karuru6225/car-iot-services/car_iot_android/DESIGN.md

# UIデザインの指針（car_iot_android）

このアプリのUIを作り直す/拡張するときの指針。2026/08のデザイン刷新で、**配色を3回
作り直して**ようやく形になった過程で得たものを残す。同じ回り道を繰り返さないための文書。

対象読者は、このリポジトリでUIを触るエージェント/開発者。

---

## 0. 前提: このアプリの被写体

**走行中に一瞥して読む車載計器**。デスクでじっくり眺める管理画面ではない。

この一文が全ての判断の根拠になる。迷ったら「実車の計器はどうなっているか」に戻る。

---

## 1. 3回失敗した記録（読み飛ばさないこと）

| 版 | やったこと | なぜ駄目だったか |
|---|---|---|
| 1. レーシング/ミニマル | Material3の`ColorScheme`だけ差し替え | ウィジェットは標準のまま。ピル型ボタン・太いProgressIndicatorが残り「Material3そのまま」の印象を脱していない |
| 2. shadcn/ui | 公式トークンをOKLCHから変換して忠実に移植 | 体系としては正しく動いたが、**Web管理画面のデザイン言語を車載計器に持ち込んだ**結果、グレー一色の事務的なUIになった |
| 3. 計器盤ベース（現行） | 形・タイポ・配色を計器の語彙で作り直し | — |

**1と2に共通する失敗**: 「数値を見せる計器」ではなく「**数値も出る設定アプリ**」を
作っていた。ラベル11sp・数値22〜30spと差が小さく、数値が主役になっていなかった。

デザインシステムを持ってくること自体は悪くない。**被写体と噛み合うかを先に問う**こと。

---

## 2. 形が先、色が後

配色だけ変えてもMaterial3の印象は抜けない。実際に効いたのは形の方だった。

- **Material3の`Button`は`Shapes`ではなく`CircleShape`固定**。テーマ側で`Shapes`を
  差し替えてもピル型のまま変わらない。`shape = ClusterButtonShape`を各ボタンに明示的に
  渡す必要がある（ハマりどころ）
- **`LinearProgressIndicator`/`CircularProgressIndicator`は使わない**。あれは「進捗」の
  表現で、計測値に進捗の概念は無い（電圧は0%から100%へ進行しない）。太い塗り面が
  数値より目立つのも良くない。レンジ内の位置は`ValueRail`（1dpのヘアライン＋2dpの
  ティック）で示す
- **テーマは配色だけでなく描かれ方も切り替えられる**。`InstrumentStyle`
  （FLAT/ANALOG）を`CompositionLocal`で配り、GAUGEテーマだけ針と目盛りのアナログ
  ダイヤルになる。ただしユーザーが選ぶゲージ種別（CIRCULAR/BAR等）は上書きしない。
  「CIRCULARが**どう描かれるか**」だけをテーマが決める

---

## 3. タイポグラフィの落差が核

計器盤は**極小のラベル**と**巨大な数値**の落差で出来ている。ここを最大に開く。

```
ラベル   10sp / letterSpacing +2.5sp   （小さく、字間を空ける）
ヒーロー 60sp / letterSpacing -2sp     （大きく、字間を詰める）
```

- 数値は**等幅かつ細字**。桁が動かず、大きくしても圧迫感が出ない。太字は使わない
  （アナログ計器の数字は太くない）
- **単位は数値に従属**する情報。極小・くすませてベースラインに沿わせる。数値と同じ
  大きさで出すとせっかくの落差が崩れる

---

## 4. 量産されがちな配色を避ける

いま生成されるUIは配色が3パターンに収束しがち:

1. クリーム地（#F4F1EA付近）＋高コントラストのセリフ＋テラコッタ
2. ほぼ黒の地＋鮮やかなアシッドグリーン/バーミリオン1色
3. ブロードシート風（ヘアライン罫・角丸ゼロ・新聞的な段組）

**被写体由来の語彙を使えば自然に外れる。** このアプリでは「夜間の自動車メーター照明は
実際に暖色アンバー」という事実からアンバーを選んだ。地色を純黒でなく青みのある
`#06080C`にしたのも、クラスターがガラス越しに冷たく沈んで見えることに倣ったもの。

---

## 5. 意味のない装飾は入れない

構造や装飾は**内容について本当のことを符号化**しているときだけ置く。

実際に**入れなかった**もの:

- **レッドゾーン** … タコメーターらしさは出るが、電圧や水温では「上限側＝危険」という
  意味を持たない。意味のない装飾になる
- クローム風グラデーション/ガラスの映り込み/針の影 … 質感の演出であって情報ではない

逆に**入れた**もの（意味があるから）:

- 主目盛り/副目盛りの階層と、**実際に刻まれた数字** … これが計器に見えるかを決める。
  円弧に棒を1本生やしただけでは円いプログレスバーにしか見えない
- 目盛りの数字を**キリのいい値に丸める** … 実レンジを素直に4等分すると
  0/1750/3500/5250/7000と半端になる。実車の計器は0/2000/4000/6000/8000のような
  刻みを持ち、そのぶん上限がレンジより広い（7000rpmの車に0-8000の文字盤）

---

## 6. プレースホルダー状態だけで判断しない

BLE未接続だと計測値は常にnullで、`--.---`しか見られない。**この状態でデザインの
良し悪しは判断できない。**

`CONTEXT.md`の「エミュレータでUIを確認する際のダミー値注入」に手順がある。要点:

- `state/CarIotState.kt`の`_measurement`/`_obdReading`/`_obdHistory`の初期値を一時的に書き換える
- `meter/MeterConfigStore.kt`の`load()`冒頭で`defaultSlots()`を即returnさせると
  ゲージ4種を一度に確認できる
- 注入行には必ず`// TODO: デザイン確認用ダミー値(戻すこと)`を付け、撤去後に
  `grep -rn "デザイン確認用" app/src/` と `git status` の**両方**で確認する

この手法で実際に見つけた不具合:

- 円弧ゲージが描画ボックスをはみ出して下半分が切れていた（プレースホルダーでは気づけない）
- 単位が数値と同じ大きさで出てラベル/数値の落差が崩れていた
- ミニグラフがほぼ平坦な直線だった（後述）

---

## 7. 視認性は数値で検証する（WCAG）

感覚で決めない。詳細は`CONTEXT.md`の「配色はWCAGのコントラスト比で検証する」。

| 対象 | 必要比 |
|---|---|
| 数値（大きい文字） | 3.0:1 |
| ラベル・本文・見出し・ボタン文字 | 4.5:1 |
| レール軌道・針・ティック・ボタン枠 | 3.0:1 |

**この検証で分かった重要な点:**

- **暗色同士の破綻は目視で気づけない**。ユーザーが気づいたのはDAYの3.50:1だったが、
  実際にはNIGHTのレールが**1.17:1**でほぼ不可視だった。全テーマで数値を出すこと
- **アクセント色を小さな文字に使うのは脆い**。DAY/GAUGEでは、見出しが4.5:1を満たす
  明度とボタン文字（白）が4.5:1を満たす明度が**両立しなかった**。アクセントは
  **図形（針・ティック）と塗りボタンに限定**し、見出し・値は前景色にする。
  実際の計器も刻印は白で色が乗るのは針だけなので、語彙としても整合する
- 比較する背景は**実際に乗る面**を使う。`Card`は`surfaceContainerHighest`、
  `OutlinedCard`と画面地は`surface`。`background`と比べても意味がない

---

## 8. フォントサイズ設定への耐性（WCAG 1.4.4）

`adb shell settings put system font_scale 1.5`（戻すときは`1.0`）で確認する。
計算では出ないので実際に拡大して見るしかない。

1.5倍で見つかった不具合:

- **数値が黙って切り捨てられていた**。`maxLines = 1`の既定overflowは`Clip`なので
  `13.812`が`13.81`になり省略記号も出ない。**崩れて見えるのではなく「別の正しそうな値」
  に見える**ため、計測値としては誤読を生む。`AutoSizeValueText`で枠に収まるまで縮小し、
  全桁を残す
- **Canvasの文字だけ拡大しなかった**。`android.graphics.Paint`の`textSize`に`dp`を
  渡していたため。**文字サイズは必ず`sp`**。ただし文字盤のように直径が決まっている
  場合は上限で頭打ちにしないと突き破る

固定幅のタイルに数値を出す箇所を追加するときは、この2点を必ず確認すること。

---

## 9. データ可視化はデータのレンジに合わせる

ミニグラフ（スパークライン）の縦軸に**メーターのレンジを使ってはいけない**。

ECU電圧のレンジは10-16Vだが実走行の揺れは13.8-14.4V程度で、レンジ基準だとグラフ
高さの1割しか使わず**ほぼ平坦な直線**にしかならない。ミニグラフは絶対値ではなく
**変化の形**を見るためのもの（絶対値はすぐ上に数値で出ている）。

ただし完全にデータ任せにすると、値がほぼ一定のときにセンサーノイズが画面いっぱいの
山脈に化ける。**メーターレンジの2%を下限の振れ幅として確保**し、それ以下の変動は
平坦なままにする。

---

## 10. 進め方

1. **被写体を一文で言う**。「走行中に一瞥して読む車載計器」。ここから全部を導く
2. **実物の語彙を調べる**。色・形・比率・書体。思いつきより実在の参照が強い
3. **形から作る**。配色だけ変えても印象は変わらない
4. **ダミー値を入れて見る**。プレースホルダーでは判断できない
5. **スクリーンショットを撮って自己批評する**。文章で考えるより早く欠陥が見つかる
6. **数値で検証する**。コントラスト比、フォントスケール1.5倍
7. **一つ減らす**。装飾を足す前に、意味を持たない要素を外せないか見る

`frontend-design`スキルが入っている環境ならそれも使う。ただし**スキルを呼ぶだけでは
足りない** — 被写体の語彙を自分で調べ、スクリーンショットで自己批評する工程が要る。

---

## 参照

- `CONTEXT.md` — 実装状態・実機検証メモ・ダミー注入とWCAG検証の具体手順
- `docs/car_iot_android_plan.md` — 全体設計・フェーズのロードマップ・刷新の経緯
- `ui/theme/` — 3テーマの配色・タイポ・角丸の定義
- `ui/meter/AnalogDial.kt` — 目盛りと針の描き方（何を描き、何を描かないか）
- `ui/meter/ValueRail.kt` — 署名要素。ProgressIndicatorを置き換えた理由
