karuru6225/car-iot-services/esp32_iot_gateway/OBD_PID_WIKIPEDIA.md

# OBD-II PID リファレンス（Wikipedia 日本語訳）

出典: [Wikipedia - OBD-II PIDs](https://en.wikipedia.org/wiki/OBD-II_PIDs)（SAE J1979 / ISO 15031-5 準拠）

> **注意**: メーカーはすべてのサービス・PID をサポートする義務はない。
> Honda N-VAN 固有の対応状況は `OBD.md` および `CAN_REFERENCE.md` を参照。

---

## 変数の定義

レスポンスバイトは A（最初）、B、C、D の順で参照する。

| 変数 | 意味 |
|---|---|
| A | レスポンス data[3]（最初のデータバイト） |
| B | レスポンス data[4] |
| C | レスポンス data[5] |
| D | レスポンス data[6] |

---

## Mode 01 — 現在データ取得（Show Current Data）

リクエスト: `Byte0=0x02 Byte1=0x01 Byte2=PID`  
レスポンス: `Byte1=0x41 Byte2=PID Byte3=A Byte4=B ...`

### 0x00〜0x1F

| PID | バイト数 | 名称 | 最小 | 最大 | 単位 | デコード式 |
|-----|---|---|---|---|---|---|
| 0x00 | 4 | サポートPID一覧 [0x01〜0x20] | — | — | — | ビットマスク |
| 0x01 | 4 | 診断コード消去後のモニタ状態 | — | — | — | ビットエンコード |
| 0x02 | 2 | フリーズフレームを記録させたDTC | — | — | — | Service 03 と同形式 |
| 0x03 | 2 | 燃料システム状態 | — | — | — | 列挙値 |
| 0x04 | 1 | 計算エンジン負荷 | 0 | 100 | % | `A / 2.55` |
| 0x05 | 1 | エンジン冷却水温 | -40 | 215 | °C | `A - 40` |
| 0x06 | 1 | 短期燃料トリム Bank1 | -100 | 99.2 | % | `(A / 1.28) - 100` |
| 0x07 | 1 | 長期燃料トリム Bank1 | -100 | 99.2 | % | `(A / 1.28) - 100` |
| 0x08 | 1 | 短期燃料トリム Bank2 | -100 | 99.2 | % | `(A / 1.28) - 100` |
| 0x09 | 1 | 長期燃料トリム Bank2 | -100 | 99.2 | % | `(A / 1.28) - 100` |
| 0x0A | 1 | 燃料圧力（ゲージ圧） | 0 | 765 | kPa | `3 × A` |
| 0x0B | 1 | 吸気管絶対圧（MAP） | 0 | 255 | kPa | `A` |
| 0x0C | 2 | エンジン回転数（RPM） | 0 | 16383.75 | rpm | `(256A + B) / 4` |
| 0x0D | 1 | 車速 | 0 | 255 | km/h | `A` |
| 0x0E | 1 | 点火タイミング進角 | -64 | 63.5 | °BTDC | `(A / 2) - 64` |
| 0x0F | 1 | 吸気温度 | -40 | 215 | °C | `A - 40` |
| 0x10 | 2 | MAF 空気流量 | 0 | 655.35 | g/s | `(256A + B) / 100` |
| 0x11 | 1 | スロットル開度 | 0 | 100 | % | `A / 2.55` |
| 0x12 | 1 | セカンダリエアシステム状態 | — | — | — | 列挙値 |
| 0x13 | 1 | O2 センサ搭載位置（2バンク） | — | — | — | ビットエンコード |
| 0x14 | 2 | O2 センサ1: 電圧 / 短期燃料トリム | 0 / -100 | 1.275 / 99.2 | V / % | `A / 200`（電圧）; `(B / 1.28) - 100`（トリム） |
| 0x15 | 2 | O2 センサ2: 電圧 / STFT | 同上 | 同上 | V / % | 同上 |
| 0x16 | 2 | O2 センサ3: 電圧 / STFT | 同上 | 同上 | V / % | 同上 |
| 0x17 | 2 | O2 センサ4: 電圧 / STFT | 同上 | 同上 | V / % | 同上 |
| 0x18 | 2 | O2 センサ5: 電圧 / STFT | 同上 | 同上 | V / % | 同上 |
| 0x19 | 2 | O2 センサ6: 電圧 / STFT | 同上 | 同上 | V / % | 同上 |
| 0x1A | 2 | O2 センサ7: 電圧 / STFT | 同上 | 同上 | V / % | 同上 |
| 0x1B | 2 | O2 センサ8: 電圧 / STFT | 同上 | 同上 | V / % | 同上 |
| 0x1C | 1 | 準拠OBD規格 | 1 | 250 | — | 列挙値 |
| 0x1D | 1 | O2 センサ搭載位置（4バンク） | — | — | — | ビットエンコード |
| 0x1E | 1 | 補助入力状態 | — | — | — | ビットエンコード |
| 0x1F | 2 | エンジン始動後経過時間 | 0 | 65535 | s | `256A + B` |

### 0x20〜0x3F

| PID | バイト数 | 名称 | 最小 | 最大 | 単位 | デコード式 |
|-----|---|---|---|---|---|---|
| 0x20 | 4 | サポートPID一覧 [0x21〜0x40] | — | — | — | ビットマスク |
| 0x21 | 2 | MIL 点灯中の走行距離 | 0 | 65535 | km | `256A + B` |
| 0x22 | 2 | 燃料レール圧力（マニホールド相対） | 0 | 5177.265 | kPa | `0.079 × (256A + B)` |
| 0x23 | 2 | 燃料レールゲージ圧（ディーゼル/GDI） | 0 | 655350 | kPa | `10 × (256A + B)` |
| 0x24 | 4 | O2 センサ1: 空燃比λ / 電圧 | — | — | ratio / V | `(2/65536) × (256A+B)`（λ）; `(8/65536) × (256C+D)`（V） |
| 0x25 | 4 | O2 センサ2: λ / 電圧 | — | — | ratio / V | 同上 |
| 0x26 | 4 | O2 センサ3: λ / 電圧 | — | — | ratio / V | 同上 |
| 0x27 | 4 | O2 センサ4: λ / 電圧 | — | — | ratio / V | 同上 |
| 0x28 | 4 | O2 センサ5: λ / 電圧 | — | — | ratio / V | 同上 |
| 0x29 | 4 | O2 センサ6: λ / 電圧 | — | — | ratio / V | 同上 |
| 0x2A | 4 | O2 センサ7: λ / 電圧 | — | — | ratio / V | 同上 |
| 0x2B | 4 | O2 センサ8: λ / 電圧 | — | — | ratio / V | 同上 |
| 0x2C | 1 | EGR 指令値 | 0 | 100 | % | `A / 2.55` |
| 0x2D | 1 | EGR エラー | -100 | 99.2 | % | `(A / 1.28) - 100` |
| 0x2E | 1 | エバポパージ指令値 | 0 | 100 | % | `A / 2.55` |
| 0x2F | 1 | 燃料タンク残量 | 0 | 100 | % | `A / 2.55` |
| 0x30 | 1 | コード消去後のウォームアップ回数 | 0 | 255 | — | `A` |
| 0x31 | 2 | コード消去後の走行距離 | 0 | 65535 | km | `256A + B` |
| 0x32 | 2 | エバポシステム蒸気圧 | -8192 | 8191.75 | Pa | `(256A + B) / 4`（符号付き） |
| 0x33 | 1 | 大気圧（絶対） | 0 | 255 | kPa | `A` |
| 0x34 | 4 | O2 センサ1: λ / 電流 | 0 / -128 | <2 / <128 | ratio / mA | `(2/65536) × (256A+B)`（λ）; `((256C+D)/256) - 128`（mA） |
| 0x35 | 4 | O2 センサ2: λ / 電流 | — | — | ratio / mA | 同上 |
| 0x36 | 4 | O2 センサ3: λ / 電流 | — | — | ratio / mA | 同上 |
| 0x37 | 4 | O2 センサ4: λ / 電流 | — | — | ratio / mA | 同上 |
| 0x38 | 4 | O2 センサ5: λ / 電流 | — | — | ratio / mA | 同上 |
| 0x39 | 4 | O2 センサ6: λ / 電流 | — | — | ratio / mA | 同上 |
| 0x3A | 4 | O2 センサ7: λ / 電流 | — | — | ratio / mA | 同上 |
| 0x3B | 4 | O2 センサ8: λ / 電流 | — | — | ratio / mA | 同上 |
| 0x3C | 2 | 触媒温度: Bank1 Sensor1 | -40 | 6513.5 | °C | `((256A + B) / 10) - 40` |
| 0x3D | 2 | 触媒温度: Bank2 Sensor1 | -40 | 6513.5 | °C | `((256A + B) / 10) - 40` |
| 0x3E | 2 | 触媒温度: Bank1 Sensor2 | -40 | 6513.5 | °C | 同上 |
| 0x3F | 2 | 触媒温度: Bank2 Sensor2 | -40 | 6513.5 | °C | 同上 |

### 0x40〜0x5F

| PID | バイト数 | 名称 | 最小 | 最大 | 単位 | デコード式 |
|-----|---|---|---|---|---|---|
| 0x40 | 4 | サポートPID一覧 [0x41〜0x60] | — | — | — | ビットマスク |
| 0x41 | 4 | 今回ドライブサイクルのモニタ状態 | — | — | — | ビットエンコード |
| 0x42 | 2 | コントロールモジュール電圧（ECU電圧） | 0 | 65.535 | V | `(256A + B) / 1000` |
| 0x43 | 2 | 絶対負荷値 | 0 | 25700 | % | `(100 / 255) × (256A + B)` |
| 0x44 | 2 | 指令空燃比λ | 0 | <2 | ratio | `(2 / 65536) × (256A + B)` |
| 0x45 | 1 | 相対スロットル開度 | 0 | 100 | % | `A / 2.55` |
| 0x46 | 1 | 外気温 | -40 | 215 | °C | `A - 40` |
| 0x47 | 1 | 絶対スロットル開度 B | 0 | 100 | % | `A / 2.55` |
| 0x48 | 1 | 絶対スロットル開度 C | 0 | 100 | % | `A / 2.55` |
| 0x49 | 1 | アクセルペダル位置 D | 0 | 100 | % | `A / 2.55` |
| 0x4A | 1 | アクセルペダル位置 E | 0 | 100 | % | `A / 2.55` |
| 0x4B | 1 | アクセルペダル位置 F | 0 | 100 | % | `A / 2.55` |
| 0x4C | 1 | スロットルアクチュエータ指令値 | 0 | 100 | % | `A / 2.55` |
| 0x4D | 2 | MIL 点灯時間 | 0 | 65535 | min | `256A + B` |
| 0x4E | 2 | コード消去後の経過時間 | 0 | 65535 | min | `256A + B` |
| 0x4F | 4 | 複数パラメータの最大値 | — | — | — | A; B; C; D×10 |
| 0x50 | 4 | MAF 最大空気流量 | 0 | 2550 | g/s | `A × 10` |
| 0x51 | 1 | 燃料種別 | — | — | — | 列挙値 |
| 0x52 | 1 | エタノール混合率 | 0 | 100 | % | `A / 2.55` |
| 0x53 | 2 | エバポシステム蒸気圧（絶対） | 0 | 327.675 | kPa | `(256A + B) / 200` |
| 0x54 | 2 | エバポシステム蒸気圧（符号付き） | -32768 | 32767 | Pa | `256A + B`（符号付き） |
| 0x55 | 2 | セカンダリO2 短期燃料トリム | -100 | 99.2 | % | `(A / 1.28) - 100`; `(B / 1.28) - 100` |
| 0x56 | 2 | セカンダリO2 長期燃料トリム | -100 | 99.2 | % | 同上 |
| 0x57 | 2 | セカンダリO2 短期燃料トリム（Bank3/4） | -100 | 99.2 | % | 同上 |
| 0x58 | 2 | セカンダリO2 長期燃料トリム（Bank3/4） | -100 | 99.2 | % | 同上 |
| 0x59 | 2 | 燃料レール絶対圧 | 0 | 655350 | kPa | `10 × (256A + B)` |
| 0x5A | 1 | アクセルペダル相対位置 | 0 | 100 | % | `A / 2.55` |
| 0x5B | 1 | HVバッテリー残量 | 0 | 100 | % | `A / 2.55` |
| 0x5C | 1 | エンジンオイル温度 | -40 | 210 | °C | `A - 40` |
| 0x5D | 2 | 燃料噴射タイミング | -210 | 301.992 | ° | `((256A + B) / 128) - 210` |
| 0x5E | 2 | エンジン燃料消費率 | 0 | 3212.75 | L/h | `(256A + B) / 20` |
| 0x5F | 1 | 排出ガス規制要件 | — | — | — | ビットエンコード |

### 0x60〜0x7F

| PID | バイト数 | 名称 | 最小 | 最大 | 単位 | デコード式 |
|-----|---|---|---|---|---|---|
| 0x60 | 4 | サポートPID一覧 [0x61〜0x80] | — | — | — | ビットマスク |
| 0x61 | 1 | ドライバ要求トルク | -125 | 130 | % | `A - 125` |
| 0x62 | 1 | 実際のエンジントルク | -125 | 130 | % | `A - 125` |
| 0x63 | 2 | エンジン基準トルク | 0 | 65535 | N·m | `256A + B` |
| 0x64 | 5 | エンジントルクデータ（5点） | -125 | 130 | % | `A-125`; `B-125`; `C-125`; `D-125`; `E-125` |
| 0x65 | 2 | 補助入出力サポート情報 | — | — | — | ビットエンコード |
| 0x66 | 5 | MAF センサ（拡張、2センサ） | 0 | 2047.97 | g/s | `(256B + C) / 32`（S1）; `(256D + E) / 32`（S2） |
| 0x67 | 3 | 冷却水温（拡張、2センサ） | -40 | 215 | °C | `B - 40`（S1）; `C - 40`（S2） |
| 0x68 | 3 | 吸気温センサ（拡張） | -40 | 215 | °C | `B - 40`（S1）; `C - 40`（S2） |
| 0x69 | 7 | EGR 実値/指令値/誤差 | — | — | — | — |
| 0x6A | 5 | ディーゼル吸気空気流量制御 | — | — | — | — |
| 0x6B | 5 | EGR 温度 | — | — | — | — |
| 0x6C | 5 | スロットルアクチュエータ指令制御 | — | — | — | — |
| 0x6D | 11 | 燃料圧力制御システム | — | — | — | — |
| 0x6E | 9 | 噴射圧力制御システム | — | — | — | — |
| 0x6F | 3 | ターボコンプレッサ入口圧力 | — | — | — | — |
| 0x70 | 10 | ブースト圧制御 | 0 | 2047.97 | kPa | `(256D + E) / 0.03125` |
| 0x71 | 6 | 可変ジオメトリターボ（VGT）制御 | — | — | — | — |
| 0x72 | 5 | ウェイストゲート制御 | — | — | — | — |
| 0x73 | 5 | 排気圧力 | — | — | — | — |
| 0x74 | 5 | ターボチャージャ回転数 | — | — | — | — |
| 0x75 | 7 | ターボチャージャ温度（Bank1） | — | — | — | — |
| 0x76 | 7 | ターボチャージャ温度（Bank2） | — | — | — | — |
| 0x77 | 5 | チャージエアクーラ温度（CACT） | — | — | — | — |
| 0x78 | 9 | 排気ガス温度（EGT）Bank1 | — | — | — | 専用フォーマット |
| 0x79 | 9 | 排気ガス温度（EGT）Bank2 | — | — | — | 専用フォーマット |
| 0x7A | 7 | DPF 差圧 | — | — | — | — |
| 0x7B | 7 | DPF 情報 | — | — | — | — |
| 0x7C | 9 | DPF 温度 | — | — | °C | `((256A + B) / 10) - 40` |
| 0x7D | 1 | NOx NTE 制御域状態 | — | — | — | — |
| 0x7E | 1 | PM NTE 制御域状態 | — | — | — | — |
| 0x7F | 13 | エンジン稼働時間 | — | — | s | `B×2²⁴ + C×2¹⁶ + D×2⁸ + E` |

### 0x80〜0xA9

| PID | バイト数 | 名称 | 単位 | デコード式 |
|-----|---|---|---|---|
| 0x80 | 4 | サポートPID一覧 [0x81〜0xA0] | — | ビットマスク |
| 0x81 | 41 | AECD エンジン稼働時間 #1〜#5 | — | — |
| 0x82 | 41 | AECD エンジン稼働時間 #6〜#10 | — | — |
| 0x83 | 9 | NOx センサ | — | — |
| 0x84 | 1 | マニホールド表面温度 | — | — |
| 0x85 | 10 | NOx 還元剤システム | % | `F / 2.55` |
| 0x86 | 5 | PM センサ | — | — |
| 0x87 | 5 | 吸気管絶対圧（代替） | — | — |
| 0x88 | 13 | SCR インデュースシステム | — | — |
| 0x89 | 41 | AECD 稼働時間 #11〜#15 | — | — |
| 0x8A | 41 | AECD 稼働時間 #16〜#20 | — | — |
| 0x8B | 7 | ディーゼル後処理 | — | — |
| 0x8C | 17 | O2 センサ（広域） | — | — |
| 0x8D | 1 | スロットル位置 G | % | — |
| 0x8E | 1 | エンジンフリクション | % | `A - 125` |
| 0x8F | 7 | PM センサ Bank1 & 2 | — | — |
| 0x90 | 3 | WWH-OBD 車両OBDシステム情報 | — | — |
| 0x91 | 5 | WWH-OBD 車両OBDシステム情報 | — | — |
| 0x92 | 2 | 燃料システム制御 | — | — |
| 0x93 | 3 | WWH-OBD 車両OBDカウンタ | — | — |
| 0x94 | 12 | NOx 警告・誘導システム | — | — |
| 0x98 | 9 | 排気ガス温度センサ | — | — |
| 0x99 | 9 | 排気ガス温度センサ | — | — |
| 0x9A | 6 | ハイブリッド/EV 車両システムデータ | — | — |
| 0x9B | 4 | ディーゼル排液センサデータ | % | `D / 2.55` |
| 0x9C | 17 | O2 センサデータ | — | — |
| 0x9D | 4 | エンジン燃料消費率（代替） | g/s | — |
| 0x9E | 2 | エンジン排気流量 | kg/h | — |
| 0x9F | 9 | 燃料システム使用率 | — | — |
| 0xA0 | 4 | サポートPID一覧 [0xA1〜0xC0] | — | ビットマスク |
| 0xA1 | 9 | NOx センサ補正データ | ppm | — |
| 0xA2 | 2 | シリンダ燃料噴射量 | mg/stroke | `(256A + B) / 32` |
| 0xA3 | 9 | エバポシステム蒸気圧 | Pa | — |
| 0xA4 | 4 | トランスミッション実ギア比 | ratio | `(256C + D) / 1000` |
| 0xA5 | 4 | ディーゼル排液投与指令値 | % | `B / 2` |
| 0xA6 | 4 | オドメータ | km | `(A×2²⁴ + B×2¹⁶ + C×2⁸ + D) / 10` |
| 0xA7 | 4 | NOx センサ濃度 S3 & S4 | — | — |
| 0xA8 | 4 | NOx センサ補正濃度 S3 & S4 | — | — |
| 0xA9 | 4 | ABS 無効スイッチ状態 | — | ビットエンコード |

---

## Mode 02 — フリーズフレームデータ

Mode 01 と同じ PID を使用する。ただし、返されるのは最後の DTC が記録された時点のスナップショット値。  
追加 PID: `0x02` → フリーズフレームを引き起こした DTC コード。

---

## Mode 03 — 保存済み DTC 一覧

DTCは1件あたり2バイト。5文字コードに変換する。

| ビット | 意味 |
|---|---|
| bit15-14 | カテゴリ: `00`=P（パワートレイン）, `01`=C（シャシー）, `10`=B（ボディ）, `11`=U（通信） |
| bit13-12 | サブカテゴリ（0〜3） |
| bit11-0 | 故障コード番号（16進3桁） |

例: `0x0158` → P0158（O2 センサ B1S2 高電圧）

---

## Mode 04 — 診断コード消去

DTCとフリーズフレームをすべて消去し、MIL を消灯する。データなし。

---

## Mode 05 — O2 センサモニタリング（非CAN車専用）

CAN 車では Mode 06 に統合されているため通常不要。  
32 種のテストID で O2 センサの電圧閾値（リッチ↔リーン遷移）を監視する。

---

## Mode 06 — コンポーネント・システムテスト

OBD モニタの測定結果（実測値、最小/最大閾値）を返す。車種ごとに定義が異なる。

---

## Mode 07 — 保留中 DTC（未確定コード）

現ドライブサイクル中に検出された未確定の DTC を返す（消去操作なしに自動クリアされる）。

---

## Mode 08 — コンポーネント制御

ECU のアクチュエータを直接制御するためのモード。車種・ECU 依存。

---

## Mode 09 — 車両情報取得

| PID | バイト数 | 名称 |
|-----|---|---|
| 0x00 | 4 | サポートPID一覧 [0x01〜0x20] |
| 0x01 | 1 | VIN メッセージカウント（通常=5） |
| 0x02 | 17 | VIN（車台番号） |
| 0x03 | 1 | キャリブレーションIDメッセージカウント |
| 0x04 | 16+ | キャリブレーションID |
| 0x05 | 1 | キャリブレーション検証番号メッセージカウント |
| 0x06 | 4〜16 | キャリブレーション検証番号（CVN） |
| 0x07 | 1 | 使用実績トラッキングメッセージカウント |
| 0x08 | 4〜5 | 使用実績トラッキング（火花点火エンジン用） |
| 0x09 | 1 | ECU 名メッセージカウント |
| 0x0A | 20 | ECU 名 |
| 0x0B | 4〜5 | 使用実績トラッキング（圧縮点火エンジン用） |

---

## Mode 0A — 永久 DTC（消去不可コード）

ECU に永続保存された DTC。OBD スキャナからの消去操作では消えない。  
実際の修理完了後に自動消去される。

---

## 注記

### デコード式の等価表現

Wikipedia の式とコード実装では同じ意味の書き方が複数存在する：

| Wikipedia 表記 | コード等価表現 | 備考 |
|---|---|---|
| `A / 2.55` | `A * 100 / 255` | 0〜100% の変換 |
| `(A / 1.28) - 100` | `(A - 128) * 100 / 128` | 燃料トリム |
| `A / 200` | `A * 0.005` | O2 センサ電圧 |
| `(2/65536) × (256A+B)` | `(uint32_t)(A<<8|B) * 2.0 / 65536` | λ比 |

### Honda N-VAN 固有事項

- **29ビット拡張アドレッシング必須**: `0x7DF`（11bit）には無応答
- **0x05冷却水温**: 非対応 → `0x67` Sensor1 で代替
- **0x10 MAF**: 非対応 → `0x66` Sensor1 で代替
- 詳細は [OBD.md](OBD.md) 参照
