karuru6225/car-iot-services/esp32_iot_gateway/src/provision.cpp

#include <Arduino.h>
#include <SPIFFS.h>
#include <Preferences.h>

// provision_device.ps1 で生成される。リポジトリには含めない
#include "provision_config.h"

// Amazon Root CA 1 (RSA 2048) - 固定値（2038年まで有効）
static const char AMAZON_ROOT_CA[] = R"EOF(-----BEGIN CERTIFICATE-----
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
rqXRfboQnoZsG4q5WTP468SQvvG5
-----END CERTIFICATE-----)EOF";

static bool writeFile(const char *path, const char *data)
{
  size_t dataLen = strlen(data);
  Serial.printf("  write %s (data len=%u)\n", path, dataLen);
  if (dataLen == 0)
  {
    Serial.println("ERROR: data is empty");
    return false;
  }
  File f = SPIFFS.open(path, "w");
  if (!f)
  {
    Serial.printf("ERROR: open failed: %s\n", path);
    return false;
  }
  size_t written = f.write((const uint8_t *)data, dataLen);
  f.close();
  Serial.printf("  %s: written=%u / %u\n", path, written, dataLen);
  return written == dataLen;
}

void setup()
{
  Serial.begin(115200);
  delay(1000);
  Serial.println("=== PROVISIONING START ===");
  Serial.println("=== PROVISIONING START ===");
  Serial.println("=== PROVISIONING START ===");
  Serial.println("=== PROVISIONING START ===");

  // SPIFFS マウント（未フォーマットなら自動フォーマット）
  if (!SPIFFS.begin(true))
  {
    Serial.println("ERROR: SPIFFS mount failed");
    return;
  }

  Serial.println("Writing certs to SPIFFS...");
  if (!writeFile("/certs/ca.crt", AMAZON_ROOT_CA) ||
      !writeFile("/certs/device.crt", PROV_DEVICE_CERT) ||
      !writeFile("/certs/device.key", PROV_DEVICE_KEY))
  {
    Serial.println("ERROR: cert write failed");
    return;
  }

  Serial.println("Writing mqtt_host / board_version to NVS...");
  Preferences prefs;
  prefs.begin("device", false);
  prefs.putString("mqtt_host", PROV_MQTT_HOST);
  prefs.putUChar("board_version", PROV_BOARD_VERSION);
  prefs.end();
  Serial.printf("  mqtt_host = %s\n", PROV_MQTT_HOST);
  Serial.printf("  board_version = %u\n", PROV_BOARD_VERSION);

  Serial.println("=== PROVISIONING COMPLETE ===");
}

void loop() {}
