karuru6225/car-iot-services/esp32_iot_gateway/src/device/lte.cpp

#include "lte.h"
#include "../logger.h"
#include "../config.h"
#include "../board_pins.h"
#include <esp_rom_crc.h>
#include <SPIFFS.h>

static const uint8_t LTE_RX_PIN = boardPins().gu10Pin;
static const uint8_t LTE_TX_PIN = boardPins().gu11Pin;
static const uint8_t LTE_EN_PIN = boardPins().gu1EnPin;

Lte lte;

static String readSpiffsFile(const char *path)
{
  File f = SPIFFS.open(path, "r");
  if (!f)
    return String();
  String s = f.readString();
  f.close();
  return s;
}

// ─── AT コマンドユーティリティ ────────────────────────────────────────────

String Lte::sendCmdResp(const char *cmd, uint32_t timeoutMs)
{
  SerialAT.println(cmd);
  unsigned long t = millis();
  String resp = "";
  while (millis() - t < timeoutMs)
  {
    if (SerialAT.available())
      resp += (char)SerialAT.read();
    if (resp.indexOf("OK") >= 0 || resp.indexOf("ERROR") >= 0)
      break;
  }
  resp.trim();
  logger.printf("  [AT] %s => %s\n", cmd, resp.c_str());
  return resp;
}

bool Lte::sendCmd(const char *cmd, uint32_t timeoutMs)
{
  return sendCmdResp(cmd, timeoutMs).indexOf("OK") >= 0;
}

// ─── 接続管理 ─────────────────────────────────────────────────────────────

// 圏外時、mqtt.connect()等の複数箇所が同一サイクル内で立て続けにconnect()を
// 呼ぶと60秒待ちが何重にも積み重なり、圏外の間ほぼ起きっぱなしになってしまう
// （DeepSleepの節電効果が失われる）。直近で失敗していれば待たずに即失敗を返す。
static const unsigned long CONNECT_RETRY_COOLDOWN_MS = 60000;

bool Lte::connect()
{
  if (_lastFailMs != 0 && millis() - _lastFailMs < CONNECT_RETRY_COOLDOWN_MS)
  {
    logger.println("[LTE] 直近でネットワーク登録失敗済み → 再試行を抑制");
    return false;
  }

  logger.println("[LTE] ネットワーク登録待ち（最大60秒）...");
  if (!_modem.waitForNetwork(60000))
  {
    logger.println("[LTE] ネットワーク登録失敗");
    _lastFailMs = millis();
    return false;
  }
  logger.printf("[LTE] Signal: %d\n", _modem.getSignalQuality());
  if (!_modem.gprsConnect(APN, APN_USER, APN_PASS))
  {
    logger.println("[LTE] GPRS 接続失敗");
    _lastFailMs = millis();
    return false;
  }
  _lastFailMs = 0;
  logger.printf("[LTE] IP: %s\n", _modem.localIP().toString().c_str());
  return true;
}

void Lte::disconnect()
{
  sendCmd("AT+SMDISC", 5000);
  _modem.gprsDisconnect();
}

void Lte::radioOff()
{
  sendCmd("AT+CFUN=0", 5000);
  digitalWrite(LTE_EN_PIN, LOW);
  logger.println("[LTE] 電源オフ");
}

void Lte::powerOff()
{
  String resp = sendCmdResp("AT+CPOWD=1", 5000);
  if (resp.indexOf("NORMAL POWER DOWN") >= 0)
    logger.println("[LTE] 電源オフ（正常シャットダウン）");
  else
    logger.println("[LTE] 電源オフ（強制切断）");
  digitalWrite(LTE_EN_PIN, LOW);
}

int Lte::signalQuality()
{
  return _modem.getSignalQuality();
}

bool Lte::isConnected()
{
  return _modem.isGprsConnected();
}

// ─── 証明書アップロード ───────────────────────────────────────────────────

void Lte::uploadCert(const char *filename, const char *pem)
{
  int len = strlen(pem);
  SerialAT.printf("AT+CFSWFILE=3,\"%s\",0,%d,5000\r\n", filename, len);

  unsigned long t = millis();
  String buf = "";
  bool gotPrompt = false;
  while (millis() - t < 5000)
  {
    if (SerialAT.available())
    {
      buf += (char)SerialAT.read();
      if (buf.indexOf("DOWNLOAD") >= 0)
      {
        gotPrompt = true;
        break;
      }
    }
  }
  if (!gotPrompt)
  {
    logger.printf("  [CERT] %s: no prompt\n", filename);
    return;
  }

  SerialAT.print(pem);

  unsigned long t2 = millis();
  String resp = "";
  while (millis() - t2 < 10000)
  {
    if (SerialAT.available())
      resp += (char)SerialAT.read();
    if (resp.indexOf("OK") >= 0 || resp.indexOf("ERROR") >= 0)
      break;
  }
  logger.printf("  [CERT] %s (%d bytes) => %s\n",
                filename, len, resp.indexOf("OK") >= 0 ? "OK" : "NG");
}

int Lte::fileOpen(const char *filename)
{
  sendCmd("AT+CFSINIT");
  char cmd[128];
  snprintf(cmd, sizeof(cmd), "AT+CFSGFIS=3,\"%s\"", filename);
  String resp = sendCmdResp(cmd, 5000);
  if (resp.indexOf("ERROR") >= 0)
  {
    logger.printf("[FILE] %s: not found\n", filename);
    sendCmd("AT+CFSTERM");
    return -1;
  }
  int q1 = resp.indexOf(':');
  if (q1 < 0) { sendCmd("AT+CFSTERM"); return -1; }
  int size = resp.substring(q1 + 1).toInt();
  if (size <= 0) { sendCmd("AT+CFSTERM"); return -1; }
  logger.printf("[FILE] %s: %d bytes\n", filename, size);
  return size;
}

// AT+CFSRFILE=<dir>,<name>,<mode>,<size>,<pos>
// mode=1: 指定位置から読み取り。バイナリ対応のため readBytes を使う
int Lte::fileReadChunk(const char *filename, int offset, uint8_t *buf, int maxLen)
{
  char rcmd[128];
  snprintf(rcmd, sizeof(rcmd), "AT+CFSRFILE=3,\"%s\",1,%d,%d", filename, maxLen, offset);
  logger.printf("  [AT] %s\n", rcmd);
  SerialAT.println(rcmd);

  // +CFSRFILE: <actual>\r\n<data> を受信
  unsigned long deadline = millis() + 10000;
  String        header   = "";
  int           idx = -1, nl = -1;
  while (millis() < deadline)
  {
    while (SerialAT.available())
      header += (char)SerialAT.read();
    idx = header.indexOf("+CFSRFILE:");
    if (idx >= 0)
    {
      nl = header.indexOf('\n', idx);
      if (nl >= 0) break;
    }
    delay(5);
  }
  if (idx < 0 || nl < 0)
  {
    logger.printf("[FILE] CFSRFILE timeout at %d\n", offset);
    return -1;
  }

  int actual = header.substring(idx + 10, nl).toInt();
  if (actual <= 0)
  {
    logger.printf("[FILE] CFSRFILE size=0 at %d\n", offset);
    return -1;
  }
  if (actual > maxLen)
  {
    // モデム応答の異常値（誤応答/化け）でバッファを超える書き込みを防ぐ
    logger.printf("[FILE] CFSRFILE size異常 at %d: actual=%d > maxLen=%d\n", offset, actual, maxLen);
    return -1;
  }

  // 先行データをコピー
  int preloaded = 0;
  int preStart  = nl + 1;
  int preAvail  = min((int)header.length() - preStart, actual);
  for (int i = 0; i < preAvail; i++)
    buf[preloaded++] = (uint8_t)header[preStart + i];

  // 残りを readBytes で読む（\0 に安全）
  int received = preloaded;
  if (received < actual)
  {
    SerialAT.setTimeout(10000);
    received += SerialAT.readBytes((char *)buf + preloaded, actual - preloaded);
  }

  // 末尾の OK を読み捨て
  {
    unsigned long t     = millis();
    String        trail = "";
    while (millis() - t < 3000)
    {
      while (SerialAT.available())
        trail += (char)SerialAT.read();
      if (trail.indexOf("OK") >= 0) break;
      delay(5);
    }
  }

  return (received > 0) ? received : -1;
}

void Lte::fileClose()
{
  sendCmd("AT+CFSTERM");
}

bool Lte::readFile(const char *filename, std::function<bool(const uint8_t *, size_t)> onChunk)
{
  int fileSize = fileOpen(filename);
  if (fileSize < 0) return false;

  static const int CHUNK = 4096;
  static uint8_t   chunk[CHUNK];
  int offset = 0;

  while (offset < fileSize)
  {
    int readLen = min(CHUNK, fileSize - offset);
    int got = fileReadChunk(filename, offset, chunk, readLen);
    if (got < 0)
    {
      fileClose();
      return false;
    }
    if (!onChunk(chunk, got))
    {
      fileClose();
      return false;
    }
    offset += got;
    logger.printf("[FILE] %d / %d bytes\n", offset, fileSize);
  }

  fileClose();
  return true;
}

bool Lte::deleteFile(const char *filename)
{
  sendCmd("AT+CFSINIT");
  char cmd[128];
  snprintf(cmd, sizeof(cmd), "AT+CFSDFILE=3,\"%s\"", filename);
  bool ok = sendCmd(cmd, 5000);
  sendCmd("AT+CFSTERM");
  if (ok)
    logger.printf("[FILE] 削除: %s\n", filename);
  else
    logger.printf("[FILE] 削除失敗（存在しない可能性）: %s\n", filename);
  return ok;
}

// ─── 時刻同期 ─────────────────────────────────────────────────────────────

bool Lte::syncTime()
{
  String resp = sendCmdResp("AT+CCLK?", 5000);
  int q1 = resp.indexOf('"');
  int q2 = resp.lastIndexOf('"');
  if (q1 < 0 || q2 <= q1)
  {
    logger.println("[TIME] CCLK パース失敗");
    return false;
  }

  String ts = resp.substring(q1 + 1, q2);
  if (ts.length() < 17)
    return false;

  struct tm t2 = {};
  t2.tm_year = ts.substring(0, 2).toInt() + 100;
  t2.tm_mon = ts.substring(3, 5).toInt() - 1;
  t2.tm_mday = ts.substring(6, 8).toInt();
  t2.tm_hour = ts.substring(9, 11).toInt();
  t2.tm_min = ts.substring(12, 14).toInt();
  t2.tm_sec = ts.substring(15, 17).toInt();

  int tzQuarters = 0;
  if (ts.length() > 17)
  {
    char sign = ts.charAt(17);
    tzQuarters = (sign == '+') ? ts.substring(18).toInt()
                               : -ts.substring(18).toInt();
  }

  time_t epoch = mktime(&t2) - (time_t)tzQuarters * 15 * 60;

  // 内蔵 RTC がすでに正常な時刻を持っている場合、モデムの時刻が過去に戻っているなら更新しない。
  // DeepSleep をまたいでも RTC は正しく進むため、NITZ 未受信のモデム時刻で上書きされるのを防ぐ。
  static const time_t MIN_VALID_EPOCH = 1700000000L; // 2023-11-15 以降なら有効とみなす
  time_t now = time(nullptr);
  if (now > MIN_VALID_EPOCH && epoch < now - 30)
  {
    char buf[32];
    strftime(buf, sizeof(buf), "%Y-%m-%dT%H:%M:%SZ", gmtime(&now));
    logger.printf("[TIME] モデム時刻が過去のため RTC を維持: %s\n", buf);
    return true;
  }

  struct timeval tv = {epoch, 0};
  settimeofday(&tv, NULL);

  char buf[32];
  strftime(buf, sizeof(buf), "%Y-%m-%dT%H:%M:%SZ", gmtime(&epoch));
  logger.printf("[TIME] 同期完了: %s\n", buf);
  return true;
}

// ─── セットアップ ─────────────────────────────────────────────────────────

void Lte::setup()
{
  pinMode(LTE_EN_PIN, OUTPUT);
  digitalWrite(LTE_EN_PIN, HIGH);
  delay(1000);

  logger.println("[LTE] 初期化...");
  SerialAT.begin(115200, SERIAL_8N1, LTE_RX_PIN, LTE_TX_PIN);

  // unsigned long t = millis();
  // while (millis() - t < 10000)
  // {
  //   while (SerialAT.available())
  //   {
  //     char c[] = {0, 0};
  //     c[0] = (char)SerialAT.read();
  //     logger.print(c);
  //   }
  // }
  delay(3000);
  _modem.init();
  sendCmd("ATE0");
  sendCmd("AT+CSCLK=0");
  for (int i = 0; i < 5; i++)
  {
    if (sendCmd("AT"))
    {
      logger.println("[LTE] モジュール応答 OK");
      break;
    }
    logger.println("[LTE] モジュール応答なし、再試行...");
    delay(2000);
  }
  logger.printf("[LTE] Modem: %s\n", _modem.getModemInfo().c_str());

  sendCmd("AT+CFUN=0", 5000);
  delay(2000);
  sendCmd("AT+CGDCONT=1,\"IP\",\"soracom.io\"");
  sendCmd("AT+CFUN=1", 5000);

  logger.println("[LTE] SMS Ready 待ち...");
  unsigned long t0 = millis();
  while (millis() - t0 < 15000)
  {
    if (SerialAT.available())
    {
      String line = SerialAT.readStringUntil('\n');
      if (line.indexOf("SMS Ready") >= 0)
      {
        logger.println("[LTE] SMS Ready!");
        break;
      }
    }
  }

  if (!SPIFFS.begin())
  {
    logger.println("[LTE] SPIFFS マウント失敗");
    return;
  }

  String caCert = readSpiffsFile(CERT_PATH_CA);
  String devCert = readSpiffsFile(CERT_PATH_DEVICE);
  String devKey = readSpiffsFile(CERT_PATH_KEY);

  if (caCert.isEmpty() || devCert.isEmpty() || devKey.isEmpty())
  {
    logger.printf("[LTE] 証明書ファイルなし（要プロビジョニング: %s, %s, %s）\n",
                  CERT_PATH_CA, CERT_PATH_DEVICE, CERT_PATH_KEY);
    return;
  }

  uint32_t crc = esp_rom_crc32_le(0, (const uint8_t *)caCert.c_str(), caCert.length());
  crc = esp_rom_crc32_le(crc, (const uint8_t *)devCert.c_str(), devCert.length());
  crc = esp_rom_crc32_le(crc, (const uint8_t *)devKey.c_str(), devKey.length());

  uint32_t stored = 0;
  bool needUpload = !getCertCrc(stored) || stored != crc;

  if (needUpload)
  {
    logger.printf("[LTE] 証明書アップロード中... (CRC=0x%08X)\n", crc);
    sendCmd("AT+CFSINIT");
    uploadCert("ca.crt", caCert.c_str());
    uploadCert("client.crt", devCert.c_str());
    uploadCert("client.key", devKey.c_str());
    sendCmd("AT+CFSTERM");
    sendCmdResp("AT+CSSLCFG=\"CONVERT\",2,\"ca.crt\"", 5000);
    sendCmd("AT+CSSLCFG=\"CONVERT\",1,\"client.crt\",\"client.key\"");
    setCertCrc(crc);
    logger.println("[LTE] 証明書アップロード完了");
  }
  else
  {
    logger.printf("[LTE] 証明書アップロードスキップ (CRC=0x%08X 一致)\n", crc);
  }
  sendCmd("AT+CSSLCFG=\"sslversion\",0,3");

  if (connect())
    syncTime();
}
