karuru6225/car-iot-services/esp32_iot_gateway/src/infra/ota.cpp

#include "ota.h"
#include "lte.h"
#include "logger.h"
#include "device.h"
#include "../config.h"
#include <esp_ota_ops.h>
#include <ArduinoJson.h>

Ota ota;

bool Ota::apply(const char *url)
{
  const esp_partition_t *partition = esp_ota_get_next_update_partition(NULL);
  if (!partition) {
    logger.println("[OTA] 更新パーティションなし");
    return false;
  }
  logger.printf("[OTA] 書き込み先: %s\n", partition->label);

  esp_ota_handle_t handle;
  esp_err_t err = esp_ota_begin(partition, OTA_SIZE_UNKNOWN, &handle);
  if (err != ESP_OK) {
    logger.printf("[OTA] begin 失敗: 0x%x\n", err);
    return false;
  }

  size_t written = 0;
  int status = lte.httpGetOta(url, [&](const uint8_t *data, size_t len) -> bool {
    esp_err_t e = esp_ota_write(handle, data, len);
    if (e != ESP_OK) {
      logger.printf("[OTA] write 失敗: 0x%x\n", e);
      return false;
    }
    written += len;
    logger.printf("[OTA] %u bytes 書き込み済み\n", written);
    return true;
  });

  if (status != 200) {
    esp_ota_abort(handle);
    logger.printf("[OTA] ダウンロード失敗 (HTTP %d)\n", status);
    return false;
  }

  err = esp_ota_end(handle);
  if (err != ESP_OK) {
    logger.printf("[OTA] 検証失敗: 0x%x\n", err);
    return false;
  }

  err = esp_ota_set_boot_partition(partition);
  if (err != ESP_OK) {
    logger.printf("[OTA] boot partition 設定失敗: 0x%x\n", err);
    return false;
  }

  logger.printf("[OTA] 完了 (%u bytes) → 再起動\n", written);
  delay(500);
  esp_restart();
  return true; // unreachable
}

void Ota::confirmBoot()
{
  const esp_partition_t *running = esp_ota_get_running_partition();
  esp_ota_img_states_t state;
  if (esp_ota_get_state_partition(running, &state) != ESP_OK) return;
  if (state != ESP_OTA_IMG_PENDING_VERIFY) return;
  esp_ota_mark_app_valid_cancel_rollback();
  logger.println("[OTA] 起動確認完了");
}

bool Ota::updateJobStatus(const char *jobId, const char *status, const char *reason)
{
  char topic[160];
  snprintf(topic, sizeof(topic),
    "$aws/things/%s/jobs/%s/update", getDeviceId(), jobId);

  char payload[256];
  if (reason) {
    snprintf(payload, sizeof(payload),
      "{\"status\":\"%s\",\"statusDetails\":{\"reason\":\"%s\"}}", status, reason);
  } else {
    snprintf(payload, sizeof(payload), "{\"status\":\"%s\"}", status);
  }

  return lte.publish(topic, payload);
}

void Ota::reportPendingJobResult()
{
  char jobId[64] = {};
  if (!getPendingJobId(jobId, sizeof(jobId))) return;

  const esp_partition_t *running = esp_ota_get_running_partition();
  esp_ota_img_states_t state;
  bool isNewFirmware = (esp_ota_get_state_partition(running, &state) == ESP_OK)
                       && (state == ESP_OTA_IMG_PENDING_VERIFY);

  if (isNewFirmware) {
    updateJobStatus(jobId, "SUCCEEDED");
    esp_ota_mark_app_valid_cancel_rollback();
    logger.printf("[OTA] ジョブ %s: SUCCEEDED・起動確認完了\n", jobId);
  } else {
    updateJobStatus(jobId, "FAILED", "rollback");
    logger.printf("[OTA] ジョブ %s: FAILED（ロールバック検出）\n", jobId);
  }

  clearPendingJobId();
}

bool Ota::check()
{
  reportPendingJobResult();

  char acceptedTopic[128], rejectedTopic[128], getTopic[128];
  snprintf(acceptedTopic, sizeof(acceptedTopic),
    "$aws/things/%s/jobs/$next/get/accepted", getDeviceId());
  snprintf(rejectedTopic, sizeof(rejectedTopic),
    "$aws/things/%s/jobs/$next/get/rejected", getDeviceId());
  snprintf(getTopic, sizeof(getTopic),
    "$aws/things/%s/jobs/$next/get", getDeviceId());

  if (!lte.subscribe(acceptedTopic)) return false;
  lte.subscribe(rejectedTopic);

  if (!lte.publish(getTopic, "{}")) return false;

  char recvTopic[128];
  static char payload[1024];
  if (!lte.pollMqtt(recvTopic, sizeof(recvTopic), payload, sizeof(payload), 5000)) {
    logger.println("[OTA] Jobs レスポンスなし");
    return false;
  }

  if (strstr(recvTopic, "rejected")) {
    logger.println("[OTA] Jobs リクエスト拒否");
    return false;
  }

  JsonDocument doc;
  DeserializationError err = deserializeJson(doc, payload);
  if (err) {
    logger.printf("[OTA] JSON パース失敗: %s\n", err.c_str());
    return false;
  }

  JsonObject exec = doc["execution"];
  if (exec.isNull()) {
    logger.println("[OTA] 更新ジョブなし");
    return false;
  }

  const char *jobId   = exec["jobId"];
  const char *version = exec["jobDocument"]["version"];
  const char *url     = exec["jobDocument"]["url"];

  if (!jobId || !url) {
    logger.println("[OTA] jobId または url が見つからない");
    return false;
  }

  // 現在と同じバージョンならスキップ
  if (version && strncmp(FIRMWARE_VERSION, version, strlen(version)) == 0) {
    logger.printf("[OTA] 同一バージョン (%s)、スキップ\n", version);
    updateJobStatus(jobId, "SUCCEEDED");
    return false;
  }

  logger.printf("[OTA] ジョブ: %s  バージョン: %s\n", jobId, version ? version : "不明");
  logger.printf("[OTA] URL (先頭80文字): %.80s\n", url);

  updateJobStatus(jobId, "IN_PROGRESS");

  setPendingJobId(jobId);

  // url は doc のライフタイムに依存するためコピーして渡す
  static char urlBuf[768];
  strncpy(urlBuf, url, sizeof(urlBuf) - 1);
  urlBuf[sizeof(urlBuf) - 1] = '\0';

  return apply(urlBuf);
}
