karuru6225/car-iot-services/esp32_iot_gateway/src/logger.cpp

#include "logger.h"
#include "service/log_storage.h"
#include <stdarg.h>

Logger logger;

void Logger::init()
{
  Serial.begin(115200);
}

void Logger::print(const char *msg)
{
  Serial.print(msg);
}

void Logger::println(const char *msg)
{
  Serial.println(msg);
  logStorageWrite(msg);
}

void Logger::printf(const char *fmt, ...)
{
  char buf[512];
  va_list args;
  va_start(args, fmt);
  vsnprintf(buf, sizeof(buf), fmt, args);
  va_end(args);
  Serial.print(buf);
  logStorageWrite(buf);
}
