karuru6225/car-iot-services/esp32_iot_gateway/src/service/command.cpp

#include "command.h"
#include "jobs.h"
#include "../logger.h"
#include "../device/ina228.h"
#include "../config.h"
#include <cstring>

bool commandHandleJob(const JobInfo &job)
{
  logger.printf("[CMD] operation: %s\n", job.operation);

  if (strcmp(job.operation, "ah_reset") == 0)
  {
    ina228.resetCharge();
    logger.println("[CMD] ah_reset: done");
    jobsReport(job.id, "SUCCEEDED");
    return true;
  }

  logger.printf("[CMD] unknown operation: %s\n", job.operation);
  jobsReport(job.id, "FAILED", "unknown operation");
  return false;
}
