karuru6225/car-iot-services/esp32_iot_gateway/src/board_pins.h

#pragma once
#include <stdint.h>

// m5atom_power_adc 基板バージョン。platformio.ini の build_flags で指定
#ifndef BOARD_VERSION
#define BOARD_VERSION 1
#endif

// 基板の未搭載ピンを表す番兵値
static constexpr uint8_t PIN_UNUSED = 0xFF;

struct BoardPins
{
  uint8_t gu00Pin;
  uint8_t gu01Pin;
  uint8_t gu0EnPin;
  uint8_t btn0Pin;
  uint8_t btn1Pin;
  uint8_t buzzerPin;
  uint8_t sdaPin;
  uint8_t sclPin;
  uint8_t chgOnPin;
  uint8_t relay0Pin;
  uint8_t relay1Pin;
  uint8_t relay2Pin;
  uint8_t gu10Pin;
  uint8_t gu11Pin;
  uint8_t gu1EnPin;
  uint8_t pwrHoldPin; // v2のみ。自己保持回路の電源保持ピン（PIN_UNUSED = 非搭載）
  uint8_t gp2Pin;     // v2のみ。J108 I2C拡張コネクタ（PIN_UNUSED = 非搭載）
  uint8_t gp3Pin;     // v2のみ。J108 I2C拡張コネクタ（PIN_UNUSED = 非搭載）
  uint8_t gp11Pin;    // v2のみ。J107 I2C拡張コネクタ（PIN_UNUSED = 非搭載）
  uint8_t gp12Pin;    // v2のみ。J107 I2C拡張コネクタ（PIN_UNUSED = 非搭載）
};

#if BOARD_VERSION == 1
#include "board_pins_v1.h"
#elif BOARD_VERSION == 2
#include "board_pins_v2.h"
#else
#error "BOARD_VERSION must be 1 or 2"
#endif

// 現在ビルド対象の基板バージョンに対応するピン配置を返す
inline const BoardPins &boardPins() { return boardPinsData; }
