karuru6225/car-iot-services/esp32_iot_gateway/src/board_pins_v2.h

#pragma once

// m5atom_power_adc v2（自己保持回路・電源SW追加基板）のピン配置
inline constexpr BoardPins boardPinsData = {
    /* gu00Pin    */ 4,
    /* gu01Pin    */ 5,
    /* gu0EnPin   */ 6,
    /* btn0Pin    */ 26,
    /* btn1Pin    */ 33,
    /* buzzerPin  */ 34,
    /* sdaPin     */ 17,
    /* sclPin     */ 18,
    /* chgOnPin   */ 21,
    /* relay0Pin  */ 13,
    /* relay1Pin  */ 14,
    /* relay2Pin  */ 15,
    /* gu10Pin    */ 7,
    /* gu11Pin    */ 8,
    /* gu1EnPin   */ 9,
    /* pwrHoldPin */ 10,
    /* gp2Pin     */ 2,
    /* gp3Pin     */ 3,
    /* gp11Pin    */ 11,
    /* gp12Pin    */ 12,
};
