karuru6225/car-iot-services/esp32_iot_gateway/test/test_domain_telemetry/test_telemetry.cpp

#include <unity.h>
#include <string>
#include <cstring>
#include <climits>
#include "domain/telemetry.h"
#include "config.h"

extern void testSetAhOffset(int32_t v);
extern void testSetChgStartV(float v);
extern void testSetChgStopV(float v);
extern void testSetChgMinDiffV(float v);
extern void testSetDebugLogEnabled(bool v);

void setUp(void)
{
  testSetAhOffset(0);
  testSetChgStartV(12.0f);
  testSetChgStopV(14.0f);
  testSetChgMinDiffV(0.3f);
  testSetDebugLogEnabled(false);
  setCharging(false);
}
void tearDown(void) {}

// clearDesiredのtrue/false両ブランチで同じフィールド一式が出ていることを確認する。
// telemetry.cppはこの2ブランチをsnprintfで手書きコピペしており、片方だけフィールドを
// 足し忘れる/消し忘れるドリフトが起きやすい（コードレビューで指摘済み）ため、
// 「両方に全フィールドが揃っている」ことをテストで縛る。
static const char *kReportedFields[] = {
    "\"ah_offset\"", "\"chg_start_v\"", "\"chg_stop_v\"", "\"chg_min_diff_v\"",
    "\"debug_log\"", "\"charging\"", "\"override_next_mode\"", "\"continuous_until_time\"",
    "\"default_mode\"", "\"fw_version\"",
};

static void assertHasAllReportedFields(const char *json)
{
  for (const char *f : kReportedFields)
    TEST_ASSERT_NOT_NULL_MESSAGE(strstr(json, f), f);
}

static void test_build_config_payload_without_clear_desired_has_no_desired_key(void)
{
  char buf[CONFIG_PAYLOAD_SIZE];
  int len = buildConfigPayload(buf, sizeof(buf), false, nullptr);
  TEST_ASSERT_GREATER_THAN(0, len);
  assertHasAllReportedFields(buf);
  TEST_ASSERT_NULL(strstr(buf, "\"desired\""));
}

static void test_build_config_payload_with_clear_desired_adds_desired_null(void)
{
  char buf[CONFIG_PAYLOAD_SIZE];
  int len = buildConfigPayload(buf, sizeof(buf), true, nullptr);
  TEST_ASSERT_GREATER_THAN(0, len);
  assertHasAllReportedFields(buf);
  TEST_ASSERT_NOT_NULL(strstr(buf, "\"desired\":null"));
}

static void test_build_config_payload_reports_override_next_mode_as_quoted_string(void)
{
  char buf[CONFIG_PAYLOAD_SIZE];
  buildConfigPayload(buf, sizeof(buf), false, "timed_continuous");
  TEST_ASSERT_NOT_NULL(strstr(buf, "\"override_next_mode\":\"timed_continuous\""));
}

static void test_build_config_payload_reports_override_next_mode_null_by_default(void)
{
  char buf[CONFIG_PAYLOAD_SIZE];
  buildConfigPayload(buf, sizeof(buf), false, nullptr);
  TEST_ASSERT_NOT_NULL(strstr(buf, "\"override_next_mode\":null"));
}

static void test_build_config_payload_reports_continuous_until_time_as_number(void)
{
  char buf[CONFIG_PAYLOAD_SIZE];
  buildConfigPayload(buf, sizeof(buf), false, "timed_continuous", (time_t)1700000000);
  TEST_ASSERT_NOT_NULL(strstr(buf, "\"continuous_until_time\":1700000000"));
}

static void test_build_config_payload_reports_continuous_until_time_null_by_default(void)
{
  char buf[CONFIG_PAYLOAD_SIZE];
  buildConfigPayload(buf, sizeof(buf), false, nullptr);
  TEST_ASSERT_NOT_NULL(strstr(buf, "\"continuous_until_time\":null"));
}

static void test_build_config_payload_reports_default_mode_as_quoted_string(void)
{
  char buf[CONFIG_PAYLOAD_SIZE];
  buildConfigPayload(buf, sizeof(buf), false, nullptr, std::nullopt, "light_sleep");
  TEST_ASSERT_NOT_NULL(strstr(buf, "\"default_mode\":\"light_sleep\""));
}

static void test_build_config_payload_reports_default_mode_null_by_default(void)
{
  char buf[CONFIG_PAYLOAD_SIZE];
  buildConfigPayload(buf, sizeof(buf), false, nullptr);
  TEST_ASSERT_NOT_NULL(strstr(buf, "\"default_mode\":null"));
}

static void test_build_config_payload_reflects_current_config_values(void)
{
  testSetAhOffset(-42);
  testSetChgStartV(11.5f);
  setCharging(true);

  char buf[CONFIG_PAYLOAD_SIZE];
  buildConfigPayload(buf, sizeof(buf), false, nullptr);

  TEST_ASSERT_NOT_NULL(strstr(buf, "\"ah_offset\":-42"));
  TEST_ASSERT_NOT_NULL(strstr(buf, "\"chg_start_v\":11.50"));
  TEST_ASSERT_NOT_NULL(strstr(buf, "\"charging\":true"));
}

// 最長ケース（desired:null付き・全nullable項目が非null・数値が最大桁）でも
// CONFIG_PAYLOAD_SIZEに収まることを縛る。溢れるとshadow.cppは送信をスキップするため、
// reportedへのフィールド追加でここが落ちたらCONFIG_PAYLOAD_SIZEを見直すこと
static void test_build_config_payload_longest_case_fits_buffer(void)
{
  testSetAhOffset(INT32_MIN);
  testSetChgStartV(99.99f);
  testSetChgStopV(99.99f);
  testSetChgMinDiffV(99.99f);
  testSetDebugLogEnabled(false);
  setCharging(false);

  char buf[CONFIG_PAYLOAD_SIZE];
  int len = buildConfigPayload(buf, sizeof(buf), true, "timed_continuous",
                               (time_t)2147483647, "light_sleep");

  TEST_ASSERT_GREATER_THAN(0, len);
  TEST_ASSERT_LESS_THAN((int)sizeof(buf), len);
  TEST_ASSERT_NOT_NULL(strstr(buf, "\"desired\":null}}"));
}

// ─── ITelemetryEncoder（JSON版のみ。MsgPack版はesp_rom_crc32_leがESP-IDF依存で対象外）───

static void test_json_encoder_encodes_battery(void)
{
  JsonTelemetryEncoder enc;
  VoltageReading mainV{12.3f};
  VoltageReading subV{12.6f};
  PowerReading pwr{1.5f, 18.0f, 25.0f, 3.2f};

  uint8_t buf[256];
  size_t len = enc.encodeBattery(buf, sizeof(buf), mainV, subV, pwr, (time_t)1700000000);

  TEST_ASSERT_GREATER_THAN(0, (int)len);
  std::string json((char *)buf, len);
  TEST_ASSERT_NOT_NULL(strstr(json.c_str(), "\"t\":\"battery\""));
  TEST_ASSERT_NOT_NULL(strstr(json.c_str(), "\"ah\":3.2"));
}

static void test_json_encoder_encodes_thermometer(void)
{
  JsonTelemetryEncoder enc;
  ThermometerData d = {};
  strncpy(d.address, "AA:BB:CC:DD:EE:FF", sizeof(d.address) - 1);
  d.temp = 21.5f;
  d.humidity = 40;

  uint8_t buf[256];
  size_t len = enc.encodeThermometer(buf, sizeof(buf), d);

  std::string json((char *)buf, len);
  TEST_ASSERT_NOT_NULL(strstr(json.c_str(), "\"t\":\"thermometer\""));
  TEST_ASSERT_NOT_NULL(strstr(json.c_str(), "\"a\":\"AA:BB:CC:DD:EE:FF\""));
}

static void test_json_encoder_encodes_diag(void)
{
  JsonTelemetryEncoder enc;
  DiagData d = {};
  d.ts = 1700000000;
  d.resetReason = 9; // ESP_RST_BROWNOUT
  d.bootCount = 42;
  d.csq = 18;
  d.queueDropped = 3;

  uint8_t buf[PAYLOAD_SENSOR_SIZE];
  size_t len = enc.encodeDiag(buf, sizeof(buf), d, "deep_sleep");

  TEST_ASSERT_GREATER_THAN(0, (int)len);
  std::string json((char *)buf, len);
  TEST_ASSERT_NOT_NULL(strstr(json.c_str(), "\"t\":\"diag\""));
  TEST_ASSERT_NOT_NULL(strstr(json.c_str(), "\"rr\":9"));
  TEST_ASSERT_NOT_NULL(strstr(json.c_str(), "\"bc\":42"));
  TEST_ASSERT_NOT_NULL(strstr(json.c_str(), "\"csq\":18"));
  TEST_ASSERT_NOT_NULL(strstr(json.c_str(), "\"qd\":3"));
  TEST_ASSERT_NOT_NULL(strstr(json.c_str(), "\"md\":\"deep_sleep\""));
}

// 全数値フィールドが最大桁・最長モード名でも pubqueue の送信バッファ（PAYLOAD_SENSOR_SIZE）に
// 収まることを縛る。溢れるとserializeJsonが途中で切れた壊れたJSONを送ってしまう
static void test_json_encoder_diag_longest_case_fits_buffer(void)
{
  JsonTelemetryEncoder enc;
  DiagData d;
  d.ts = UINT32_MAX;
  d.bootCount = UINT32_MAX;
  d.uptimeSec = UINT32_MAX;
  d.heapFree = UINT32_MAX;
  d.heapMin = UINT32_MAX;
  d.queueDropped = UINT16_MAX;
  d.resetReason = UINT8_MAX;
  d.wakeupCause = UINT8_MAX;
  d.csq = UINT8_MAX;
  d.queueLen = UINT8_MAX;
  d.mode = UINT8_MAX;

  // 収まらない場合を検出できるよう、バッファは1バイト余分に取って書き込み長を比べる
  uint8_t buf[PAYLOAD_SENSOR_SIZE + 1];
  size_t len = enc.encodeDiag(buf, sizeof(buf), d, "timed_continuous");

  TEST_ASSERT_GREATER_THAN(0, (int)len);
  TEST_ASSERT_LESS_THAN(PAYLOAD_SENSOR_SIZE, (int)len);
  TEST_ASSERT_EQUAL('}', buf[len - 1]);
}

static void test_json_encoder_topic_suffix(void)
{
  JsonTelemetryEncoder enc;
  TEST_ASSERT_EQUAL_STRING("data", enc.topicSuffix());
}

int main(int argc, char **argv)
{
  (void)argc;
  (void)argv;
  UNITY_BEGIN();
  RUN_TEST(test_build_config_payload_without_clear_desired_has_no_desired_key);
  RUN_TEST(test_build_config_payload_with_clear_desired_adds_desired_null);
  RUN_TEST(test_build_config_payload_reports_override_next_mode_as_quoted_string);
  RUN_TEST(test_build_config_payload_reports_override_next_mode_null_by_default);
  RUN_TEST(test_build_config_payload_reports_continuous_until_time_as_number);
  RUN_TEST(test_build_config_payload_reports_continuous_until_time_null_by_default);
  RUN_TEST(test_build_config_payload_reports_default_mode_as_quoted_string);
  RUN_TEST(test_build_config_payload_reports_default_mode_null_by_default);
  RUN_TEST(test_build_config_payload_reflects_current_config_values);
  RUN_TEST(test_build_config_payload_longest_case_fits_buffer);
  RUN_TEST(test_json_encoder_encodes_battery);
  RUN_TEST(test_json_encoder_encodes_thermometer);
  RUN_TEST(test_json_encoder_encodes_diag);
  RUN_TEST(test_json_encoder_diag_longest_case_fits_buffer);
  RUN_TEST(test_json_encoder_topic_suffix);
  return UNITY_END();
}
