karuru6225/car-iot-services/m5atom_iot_gateway/infra__ble_scan.h

#pragma once
#include <BLEDevice.h>
#include <BLEScan.h>
#include <BLEAdvertisedDevice.h>
#include <freertos/FreeRTOS.h>
#include <freertos/queue.h>
#include "config.h"
#include "domain__switchbot_data.h"

class BleScanner
{
public:
  QueueHandle_t queue = nullptr;

  void setup();
  void start(int seconds);
  void clearResults();

private:
  BLEScan *_scan = nullptr;
};

extern BleScanner scanner;
